fg89o/C01CH/C01CH fw/src/fan/fanControl.h

/**
 * DomDom Firmware
 * Copyright (c) 2020 DomDomFirmware
 *

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
 */

#pragma once
#ifndef DOMDOM_FANCONTROL_h
#define DOMDOM_FANCONTROL_h

#include <Arduino.h>
#include "configuration.h"

/**
 * Clase para el control del ventilador
 * 
 * Esta clase sera la encargada de controlar el ventilador.
 * 
 */
class DomDomFanControlClass
{
    private:
        /**
         * Indica si el proceso está activado.
         */
        bool _started = false;
        /**
         * Tarea de control.
         */
        static void fanTask(void * parameter);
        /**
         * Valor de histeresis
         */
        int _histeresis;

    public:
        /**
         * Constructor.
         * */
        DomDomFanControlClass();
        /**
         * Nivel PWM para cuando el canal se encuentra en el valor máximo.
         */
        uint16_t max_pwm;
        /**
         * Nivel PWM para cuando el canal de encuentra en el valor minimo.
         */
        uint16_t min_pwm;
        /**
         * PWM actual
         */
        uint16_t curr_pwm;
        /**
         * Temperatura para el valor min_pwm
         */
        uint16_t min_channel_value;
        /**
         * Temperatura para el valor max_pwm
         */
        uint16_t max_channel_value;
        /**
         * Potencia del ventilador en porcentaje
         */
        uint8_t potencia;
        /**
         * Inicia el proceso de control del ventialdor.
         */
        void begin();
        /**
         * Para el proceso de control de ventilador.
         */
        void end();
        /**
         * Comprueba el estado actual y actualiza los valores
         */
        void update();
        /**
         * Indica si el control de ventilador esta activo
         */
        bool isStarted() const {return _started; };
        /**
         * Establece el PWM para el ventialdor
         */
        void setCurrentPWM(uint16_t pwm);
        /**
         * Guarda el estado actual en la memoria
         */
        bool save();
        /**
         * Carga los valores almacenados en memoria
         */
        bool load();
};


#if !defined(NO_GLOBAL_INSTANCES)
extern DomDomFanControlClass DomDomFanControl;
#endif

#endif /* DOMDOM_FANCONTROL_h */
