fg89o/C01CH/C01CH fw/src/EEPROMHelper.cpp

/**
 * Óscar Fernández
 * Copyright (c) 2020
 *

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
 */

#include "EEPROMHelper.h"
#include "configuration.h"
#include <EEPROM.h>

void EEPROMInit()
{
    EEPROM.write(1,1);

    /** DIRECCION EEPROM DEL WIFI */
    EEPROM.writeString(EEPROM_STA_SSID_NAME_ADDRESS, WIFI_STA_SSID_NAME);
    EEPROM.writeString(EEPROM_STA_PASSWORD_ADDRESS, WIFI_STA_PASSWORD);
    /************************************************************/
 
    /** DIRECCION EEPROM DEL SERVICIO MDNS*/
    EEPROM.write(EEPROM_MDNS_ENABLED_ADDRESS, MDNS_ENABLED);
    EEPROM.writeString(EEPROM_MDNS_HOSTNAME_ADDRESS, MDNS_HOSTNAME);
    /************************************************************/

    /** DIRECCIONES EEPROM DEL CANAL */
    int address = EEPROM_CHANNEL_FIRST_ADDRESS;
    // canal
    EEPROM.write(address,0);
    address += 1;
    // enabled
    EEPROM.write(address,0);
    address += 1;
    // INA ADDRESS
    EEPROM.writeUShort(address,0);
    address += 2;
    // TARGET VOLTS
    EEPROM.writeFloat(address,0);
    address += 4;
    // MAX miliamps
    EEPROM.writeFloat(address,0);
    address += 4;
    // MIN MILIAMPS
    EEPROM.writeFloat(address,0);
    address += 4;
    // TARGET MILIAMPS
    EEPROM.writeFloat(address,0);
    address += 4;
    // LEDS
    EEPROM.write(address,0);
    /************************************************************/

    /** DIRECCION EEPROM DE LA AGENDA */
    EEPROM.writeBool(EEPROM_SCHEDULE_STATUS_ADDRESS, true);
    /************************************************************/

    /** DIRECCIONES EEPROM DEL SERVICIO NTP */
    EEPROM.writeBool(EEPROM_NTP_ENABLED_ADDRESS, NTP_ENABLED);
    EEPROM.writeString(EEPROM_NTP_SERVERNAME_ADDRESS, NTP_SERVERNAME);
    EEPROM.writeString(EEPROM_NTP_TIMEZONENAME_ADDRESS, NTP_TIMEZONE);
    EEPROM.writeString(EEPROM_NTP_TIMEZONEPOSIX_ADDRESS, NTP_POSIX_TIMEZONE);
    /************************************************************/

    /** Confirmamos cambios */
    EEPROM.commit();
}

void EEPROMCheck()
{
    if (EEPROM.read(1) != 1)
    {
        Serial.print("Detectado primer arranque. Inicializando EEPROM\n");
        EEPROMInit();
    }
}
