fg89o/C01CH/C01CH fw/src/channel/schedulePoint.h

/**
 * DomDom Firmware
 * Copyright (c) 2020 DomDomFirmware
 *

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
 */

#pragma once
#ifndef DOMDOM_SCHEDULEPOINT_h
#define DOMDOM_SCHEDULEPOINT_h

#include <Arduino.h>

/**
 * Enumerado para los dias de la semana
 */
enum DomDomDayOfWeek
{
    DOMINGO = 1,
    LUNES = 2,
    MARTES = 4,
    MIERCOLES = 8,
    JUEVES = 16,
    VIERNES = 32,
    SABADO = 64,
    SEMANA = 62,
    FESTIVO = 65,
    ALL = 127,
};

/**
 * Punto de programacion.
 * 
 * Esta clase representa un punto de programacion.
 * Se configura una hora, un valor para cada canal y 
 * un booleano que indica si el cambio es progresivo
 * en el tiempo o no.
 */
class DomDomSchedulePoint
{
    public:
        /**
         * Constructor por defecto para un punto vacio.
         * */
        DomDomSchedulePoint();
        /**
         * Constructor para inicializar con ciertos valores.
         */
        DomDomSchedulePoint(DomDomDayOfWeek dayOfWeek, uint8_t hour, uint8_t minute, bool fade = true);
        /**
         * Constructor para inicializar con todos los valores.
         */
        DomDomSchedulePoint(DomDomDayOfWeek dayOfWeek, uint8_t hour, uint8_t minute, uint8_t value, bool fade = true);
        /**
         * Indica si el cambio es progresivo en el tiempo o no.
         */
        bool fade = true;
        /**
         * Dia de la semana a la que afecta el punto de programacion.
         * NO IMPLEMENTADO!!!!
         */
        DomDomDayOfWeek dayOfWeek;
        /**
         * Hora del punto de programacion.
         */
        uint8_t hour;
        /**
         * Minuto del punto de programacion.
         */
        uint8_t minute;
        /**
         * Valor en porcentaje (0-100%) para el canal.
         */
        uint8_t value;
};

#endif /* DOMDOM_SCHEDULEPOINT_h */
